cherking19/EC463_SmartExerciseSystem/IMG_1004.jpeg

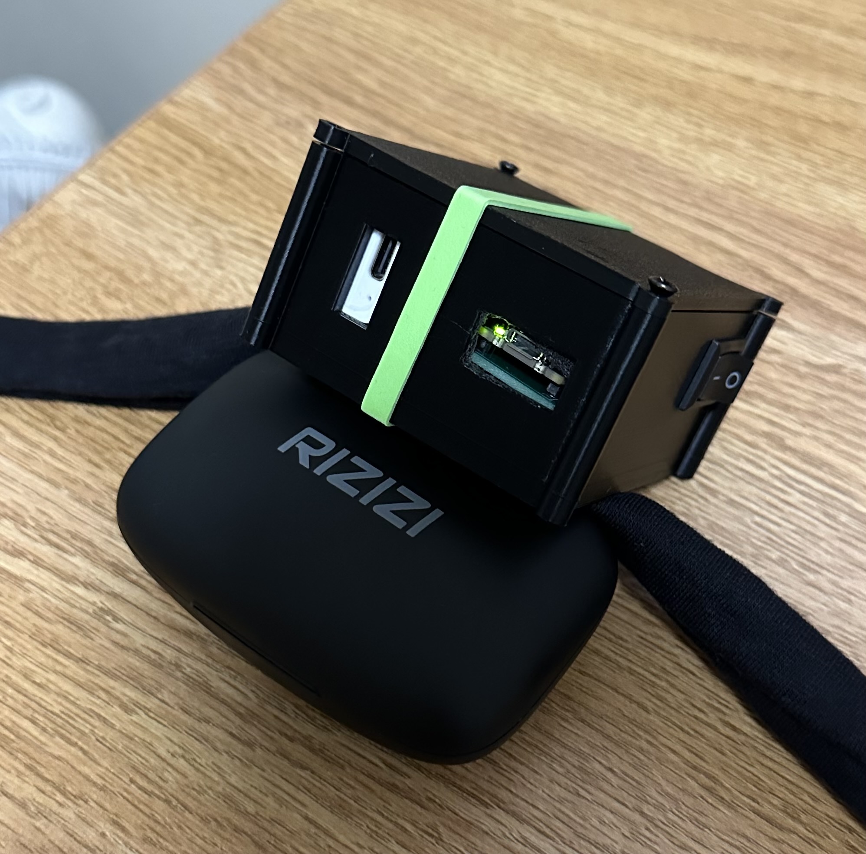
IMG_1004.jpeg
